willis936/nixie-clock-ice/hardware/LTspice/common_emitter.asc

Cload: cap; 15p
D1: diode
Ranode: res; 27k
RD: res; 100k
Rdiv1: res; 100k
Rdiv2: res; 10Meg
Rdiv3: res; 1Meg
Rdiv4: res; 10k
Rdiv5: res; 1Meg
Rdiv6: res; 47k
Rload: res; 1Meg
RS: res; 100k
U1: BSP88_L0; SiB452DK
Vnixie: voltage; PULSE(145 150 10u 1u 1u 0.1 0.1 10)
VPP: voltage; SINE(165 45 10)
Named nets: 0, Load, Anode, HV_supply, V_divider, LV_supply, Source, V_divider_2
.tran 20u
.include 1N4004RL.LIB
.include SiB452DK_PS.LIB
