willis936/nixie-clock-ice/hardware/LTspice/HV_bleed.asc

C1: cap; 10µ
C3: cap; 1µ
D1: diode; D1n4004rl
Q1: npn; MPSA42
Q2: npn; MPSA42
R1: res; 1000k
R2: res; 10k
R3: res; 10Meg
R4: res; 100k
R5: res; 4.7k
S1: sw; SW4V
S2: sw; SW4V
V1: voltage; PULSE(5 0 10m 10u 10u 10 0 1)
V2: voltage; 210
V3: voltage; PULSE(5 0 30m 10u 10u 10 0 1)
V4: voltage; 5
Named nets: 0, HV_rail, LV_rail, Gate, Drain
.tran 500m
.model SW4V SW(Ron=0.1 Roff=10Meg Vt=3.5 Vh=0.5)
.include 1N4004RL.LIB
.include MPSA42.LIB
