willis936/nixie-clock-ice/hardware/LTspice/HV_supply_tripler.asc

C1: polcap; 1µ; V=250
C2: polcap; 1µ; V=250
C3: polcap; 1µ; V=250
D1: diode; D1n4004rl
D2: diode; D1n4004rl
D3: diode; D1n4004rl
D4: zener; 1N5378B
D5: zener; 1N5378B
L1: ind; 10µ; Ipk=6 Rser=0.0195 Rpar=37085.5 Cpar=2.373p
M1: nmos; IRLH5030
RAnode: res; 4.5k
Rdiv1: res; 10Meg
Rdiv2: res; 100k
RL: res; {RLoad}
S1: sw; SWLoad
VCC: voltage; 4.75; Rser=0.01
VGate1: voltage; PULSE(0 3.3 0 {Tedge} {Tedge} {Ton} 10u); Rser=0.1
Named nets: 0, 5V_supply, 100V_BOOST, 200V_BOOST, HV_sense, 200V_supply, 100V_SUPPLY, Gate
.tran 50m
.include 1N4004RL.LIB
*.step param Ton list 5u 8u 9.8u
voltage tripler
CCM 5 to 100 V boost convertor
.include SiB452DK_PS.LIB
.param Ton=9.1u
.model SWLoad SW(Ron=0.1 Roff=100Meg Vt=150 Vh=5
.param RLoad=4.8k
*.step param RLoad list 9.7k 4.8k
.param Tedge 10n
