willis936/nixie-clock-ice/hardware/LTspice/component_check.asc

D1: diode; D1n4004rl
Q1: npn; MPSA42
RCollector: res; 10k
RDiode: res; 1k
RDrain1: res; 10k
RDrain2: res; 10k
RDrain3: res; 10k
RDrain4: res; 10k
REmitter: res; 1k
RSource1: res; 1k
RSource2: res; 1k
RSource3: res; 1k
RSource4: res; 1k
U1: BSP88_L0
U2: BSP88_L0; NMOS_SSM3K2615R
U3: rjp020n06
U4: BSP88_L0; SiB452DK
VCC: voltage; 50; Rser=0
VDrive: voltage; SINE(0 5 10 0 0 0 1k); Rser=0
Named nets: 0, LV_supply, Base/Gate, Collector, Emitter, Drain1, Source1, Drain2, Source2, Drain3, Source3, Drain4, Source4
.tran 100m
.include MPSA42.LIB
.include 1N4004RL.LIB
.include SSM3K2615R.LIB
.include SiB452DK_PS.LIB
