willis936/nixie-clock-ice/hardware/LTspice/differential_amp.asc

C1: cap; 15p
Q1: npn; MPSA42
Q2: npn; MPSA42
Q3: npn; MPSA42
R1: res; 1000k
Ranode: res; 33k
RB1: res; 10k
RC1: res; 2.2k
RC2: res; 2.2k
Rdiv1: res; 10000k
Rdiv2: res; 100k
RE1: res; 100k
RE2: res; 100k
RE3: res; 3.24k
U1: LT1634-1.25
VCC: voltage; 5
Vnixie: voltage; PULSE(145 150 10u 1u 1u 0.1 0.1 10)
VPP: voltage; 170
Named nets: 0, HV_supply, Anode, LV_supply, Load, Anode_div
.tran 20u
.include MPSA42.LIB
AoE 3E 2.3.8 differential amplifiers
G_{diff} = R_{C}/(2*(R_{E}+r_{e}))
G_{diff} = 2.2k/(2*(100k+~1)) = 0.011 = 90.~{90}
