willis936/nixie-clock-ice/hardware/LTspice/HV_supply_2stageBoost.asc

C1: cap; 10µ; V=250
C2: cap; 10µ; V=250
D1: diode; D1n4004rl
D3: diode; D1n4004rl
I1: load2; {ILoad}
L1: ind; 15µ; Ipk=2.5 Rser=0.075 Rpar=77244 Cpar=0
L2: ind; 820µ; Ipk=1.6 Rser=0.64 Rpar=77244 Cpar=0 mfg="Coilcraft" pn="MSS1583-824"
Rdiv1: res; 10000k
Rdiv2: res; 100k
RS: res; 40m
U1: BSP88_L0
U2: BSP88_L0
VCC: voltage; 5; Rser=0.01
VGate1: voltage; PULSE(0 5 0 10n 10n 3.5u 4.56621u 6000k); Rser=0.1
VGate2: voltage; PULSE(0 20 0 100n 100n 8u 10u 6000k); Rser=0.1
Named nets: 0, 5V_supply, 20V_BOOST, 20V_supply, HV_sense, HV_BOOST, HV_supply
.tran 10m
.include 1N4004RL.LIB
.step param ILoad 0.10 0.040 0.010
