willis936/nixie-clock-ice/hardware/LTspice/HV_supply_2xDoubler.asc

C1: cap; 100n; V=250
C2: cap; 10µ; V=250
C3: cap; 10µ; V=250
C4: cap; 100n; V=250
C5: cap; 10µ; V=250
D1: diode; D1n4004rl
D2: diode; D1n4004rl
D3: diode; D1n4004rl
D4: diode; D1n4004rl
D5: diode; D1n4004rl
L1: ind; 470µ; Ipk=1.4 Rser=0.437 Rpar=105259 Cpar=20.593p mfg="Würth Elektronik" pn="7447709471 WE-PD 1210"
RAnode: res; 27k
Rdiv1: res; 10000k
Rdiv2: res; 100k
U1: BSP88_L0
VCC: voltage; 4.75; Rser=0.01
VGate1: voltage; PULSE(0 5 0 10n 10n 9.1u 10u 6000k); Rser=0.1
Named nets: 0, 5V_supply, BOOST, 50V_supply, HV_sense, HV_supply
.tran 100m
.include 1N4004RL.LIB
*.step param ILoad 0.10 0.040 0.010
2x voltage doubler
DCM 5 to 50 V CCM boost convertor
.param ILoad 0.10
