willis936/nixie-clock-ice/hardware/LTspice/PWM_filter.asc

C1: cap; 100n
R1: res; 100k
R2: res; 100k
V1: voltage; PULSE(0 3.3 0 1u 1u 50u 100u); Rser=100
Named nets: 0
.tran 500m
