willis936/nixie-clock-ice/hardware/LTspice/HV_control.asc

R1: res; 100k
R2: res; 470
R3: res; 270k
R4: res; 10k
R5: res; 1.5k
R6: res; 270k
R7: res; 10k
R8: res; 1.5k
R9: res; 270k
R10: res; 10k
R11: res; 1.5k
R12: res; 270k
R13: res; 10k
R14: res; 1.5k
V1: voltage; 210
V2: voltage; 210
V3: voltage; 0
V4: voltage; 183
V5: voltage; 1
V6: voltage; 120
V7: voltage; 3.3
V8: voltage; SINE(165 45 1)
V9: voltage; SINE(1.65 1.65 1)
Named nets: 0
.tran 1
